ZigZagJoe/SillyTinySCSI/label_black.png

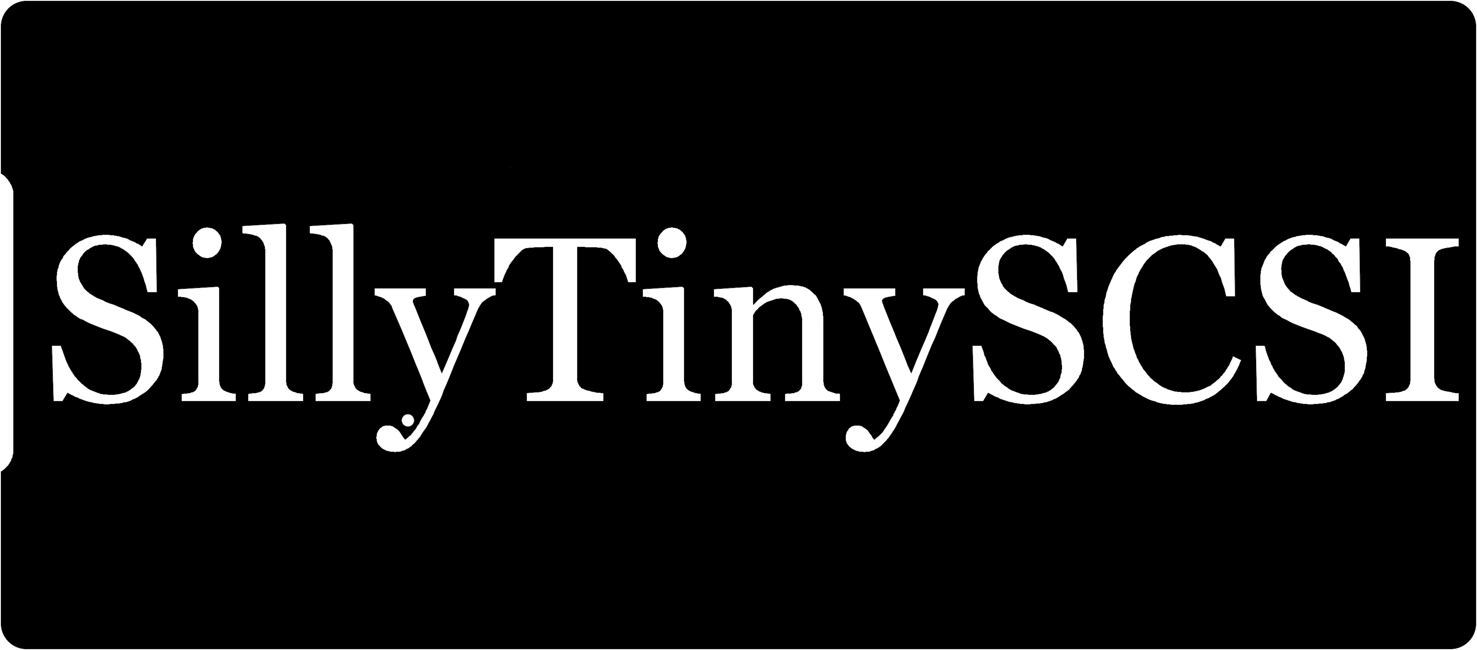
label_black.png
